MarkJB/Tester_PCB_Business_Card/software/firmware/tester_runtime/src/funconfig.h

#ifndef _FUNCONFIG_H
#define _FUNCONFIG_H

// you can put various configurations in here, you can see a full list in ch32fun.h
// part selection is made in the Makefile
#define FUNCONF_ENABLE_HPE 0

#endif
